olofos/avr-nes-synth/controller/io-bridge.h

#ifndef IO_BRIDGE_
#define IO_BRIDGE_

#define BUTTON_PRESS_RIGHT 1
#define BUTTON_PRESS_UP    2
#define BUTTON_PRESS_DOWN  3
#define BUTTON_PRESS_LEFT  4

#define BUTTON_RELEASE_RIGHT 5
#define BUTTON_RELEASE_UP    6
#define BUTTON_RELEASE_DOWN  7
#define BUTTON_RELEASE_LEFT  8

#define BUTTON_HOLD_RIGHT 9
#define BUTTON_HOLD_UP    10
#define BUTTON_HOLD_DOWN  11
#define BUTTON_HOLD_LEFT  12


uint8_t get_input();

#endif
